Davidbick/PowerMesh/Home Assistant Docs/Matter Standard.pdf

What is the Matter Standard

Matter is an open-source communication standard for smart home devices. It was created to unify proprietary smart devices such as Apple, Google, Amazon, and Samsung to talk with each other. Essentially, it allows you to mix and match smart home devices and hubs among top brands and for any other brand that adopts the Matter standard.

How Matter works

If something has the Matter standard, then it has standardized commands. This would mean a hub and a smart bulb from two different brands will share the same commands, so the bulb will understand the command sent from the hub.

For connectivity, each device should have their own IPv6 address. Matter works with Wi-Fi, thread, and Bluetooth.

Matter locality

Matter works locally first, so it doesn’t require the cloud or internet to function. If the devices receive power, the hub should be able to send commands to the smart device. The smart devices that receive the command should also function the same.

Security

[add information about distributed compliance ledger]

[add info about encryption]
