Davidbick/PowerMesh/Home Assistant Docs/Home Assistant.pdf

## Home Assistant

What it is

Home Assistant is an open-source software that is meant for home automation. Compared to other smart hubs, Home Assistant excels in privacy/security and reliability. This is because Home Assistant relies on the local area network (LAN). If the Wi-Fi is down but power is still available, Home Assistant can still issue commands over LAN. In the chance that LAN is not available, Home Assistant also works with Zigbee and Z-Wave devices which use mesh networks. Since everything is local and is not part of the cloud, it is private and secure.

Another power of Home Assistant is that since it works with Zigbee, Z-Wave, Wi-Fi, and Bluetooth, it can integrate many different products together. If a Bluetooth device is triggered, Home Assistant will be notified and can tell a Zigbee device to do something depending on that state of the Bluetooth device. This allows for powerful pairings of devices that can’t communicate with each other.

If a device only works with the cloud, Home Assistant can communicate with the cloud too, but it requires internet.

What is needed

For Home Assistant to work, it needs dedicated hardware that is always running. This can be a laptop turned into a server, a Raspberry Pi (RPI), or Home Assistant’s own hardware (Home Assistant Green or Yellow [Note: Yellow is discontinued but is still receiving software updates]). For the Raspberry Pi route, USB dongles would have to be installed for Zigbee/Z-wave and maybe even Bluetooth (since the Pi’s Bluetooth might not be strong enough). For Home Assistant Green, it works on the internet and LAN but doesn’t come with Zigbee/Z-Wave. It is essentially made for plug-and-play. Home Assistant Yellow features more capabilities like Zigbee and Z-Wave. It also supports Thread, which uses Matter. However, it costs more.

Another note for using Raspberry Pi is the difference between RPI3, RPI4, and RPI5. RPI3 can handle Home Assistant, but its capabilities are limited, such as its 1 GB of RAM. For a little more money, RPI4 is a direct upgrade to RPI3. RPI4 has the option to be bought with 4 GB which would be useful if installing apps/add-ons for Home Assistant. It also has 2 USB3 ports, which are much better than USB2. With the USB3 ports, a SATA SSD can be added with a USB to SATA connector. A SATA SSD will offer more reliability and speed compared to a MicroSD card. For the RPI5, it needs active cooling. While the RPI5 has more capabilities than the RPI4, we probably don’t need that performance for our project.

How to connect to Home Assistant

How Home Assistant get statuses of devices

Some devices may report their statuses to Home Assistant. However, some devices don’t. To get the status of these devices, Home Assistant polls the device for their status every certain amount of time.
