Davidbick/PowerMesh/General_ST_Docs/ST_Eval_Files/EVALKITST8500-1 PCB Layout/PSU_VIPER_BOARD_HV_rev251/PSU_VIPER_BOARD_HV-Rev2-assy_top+track.pdf

PCB 1

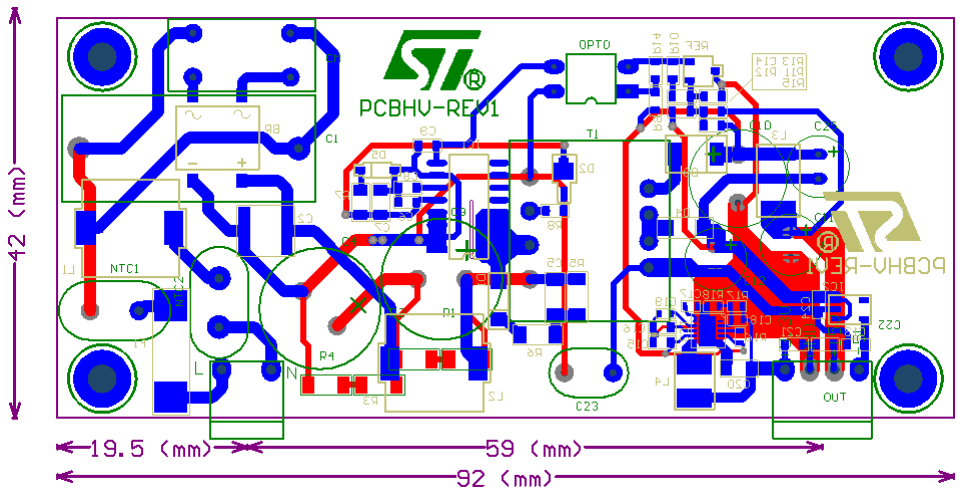
[picture p9: figure]
