Davidbick/PowerMesh/General_ST_Docs/ST_Eval_Files/EVLKST8500GH-2_Schematics/Schematic files/EVALMODST8500-1-Rev421-schematic.pdf

ST8500

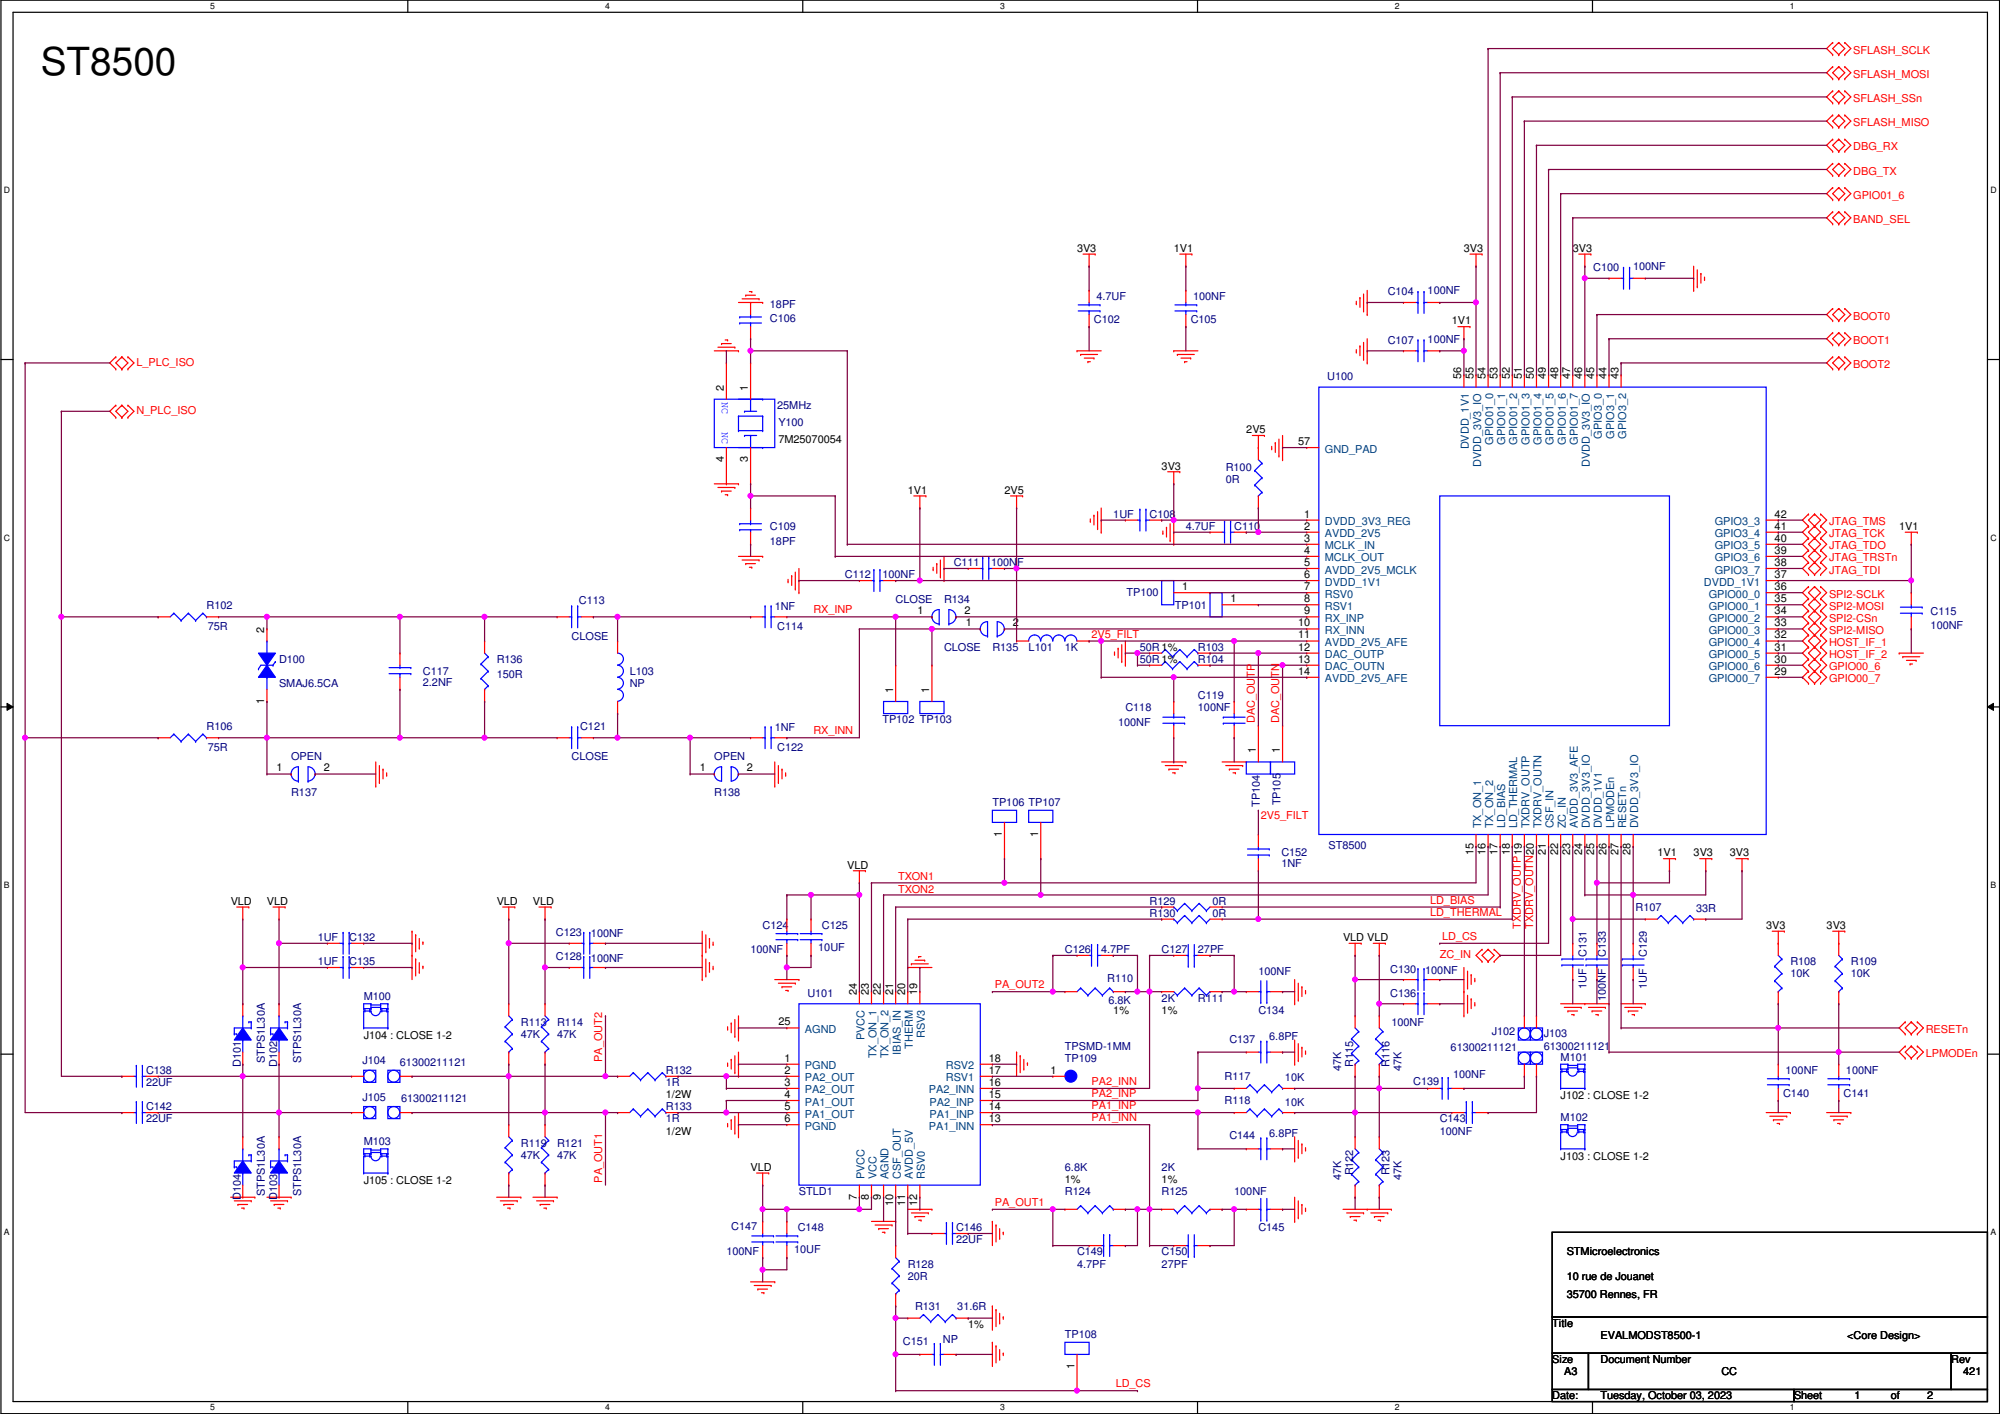
[picture p14: page 1]

# Board to Board Connector - Digital

# SERIAL FLASH

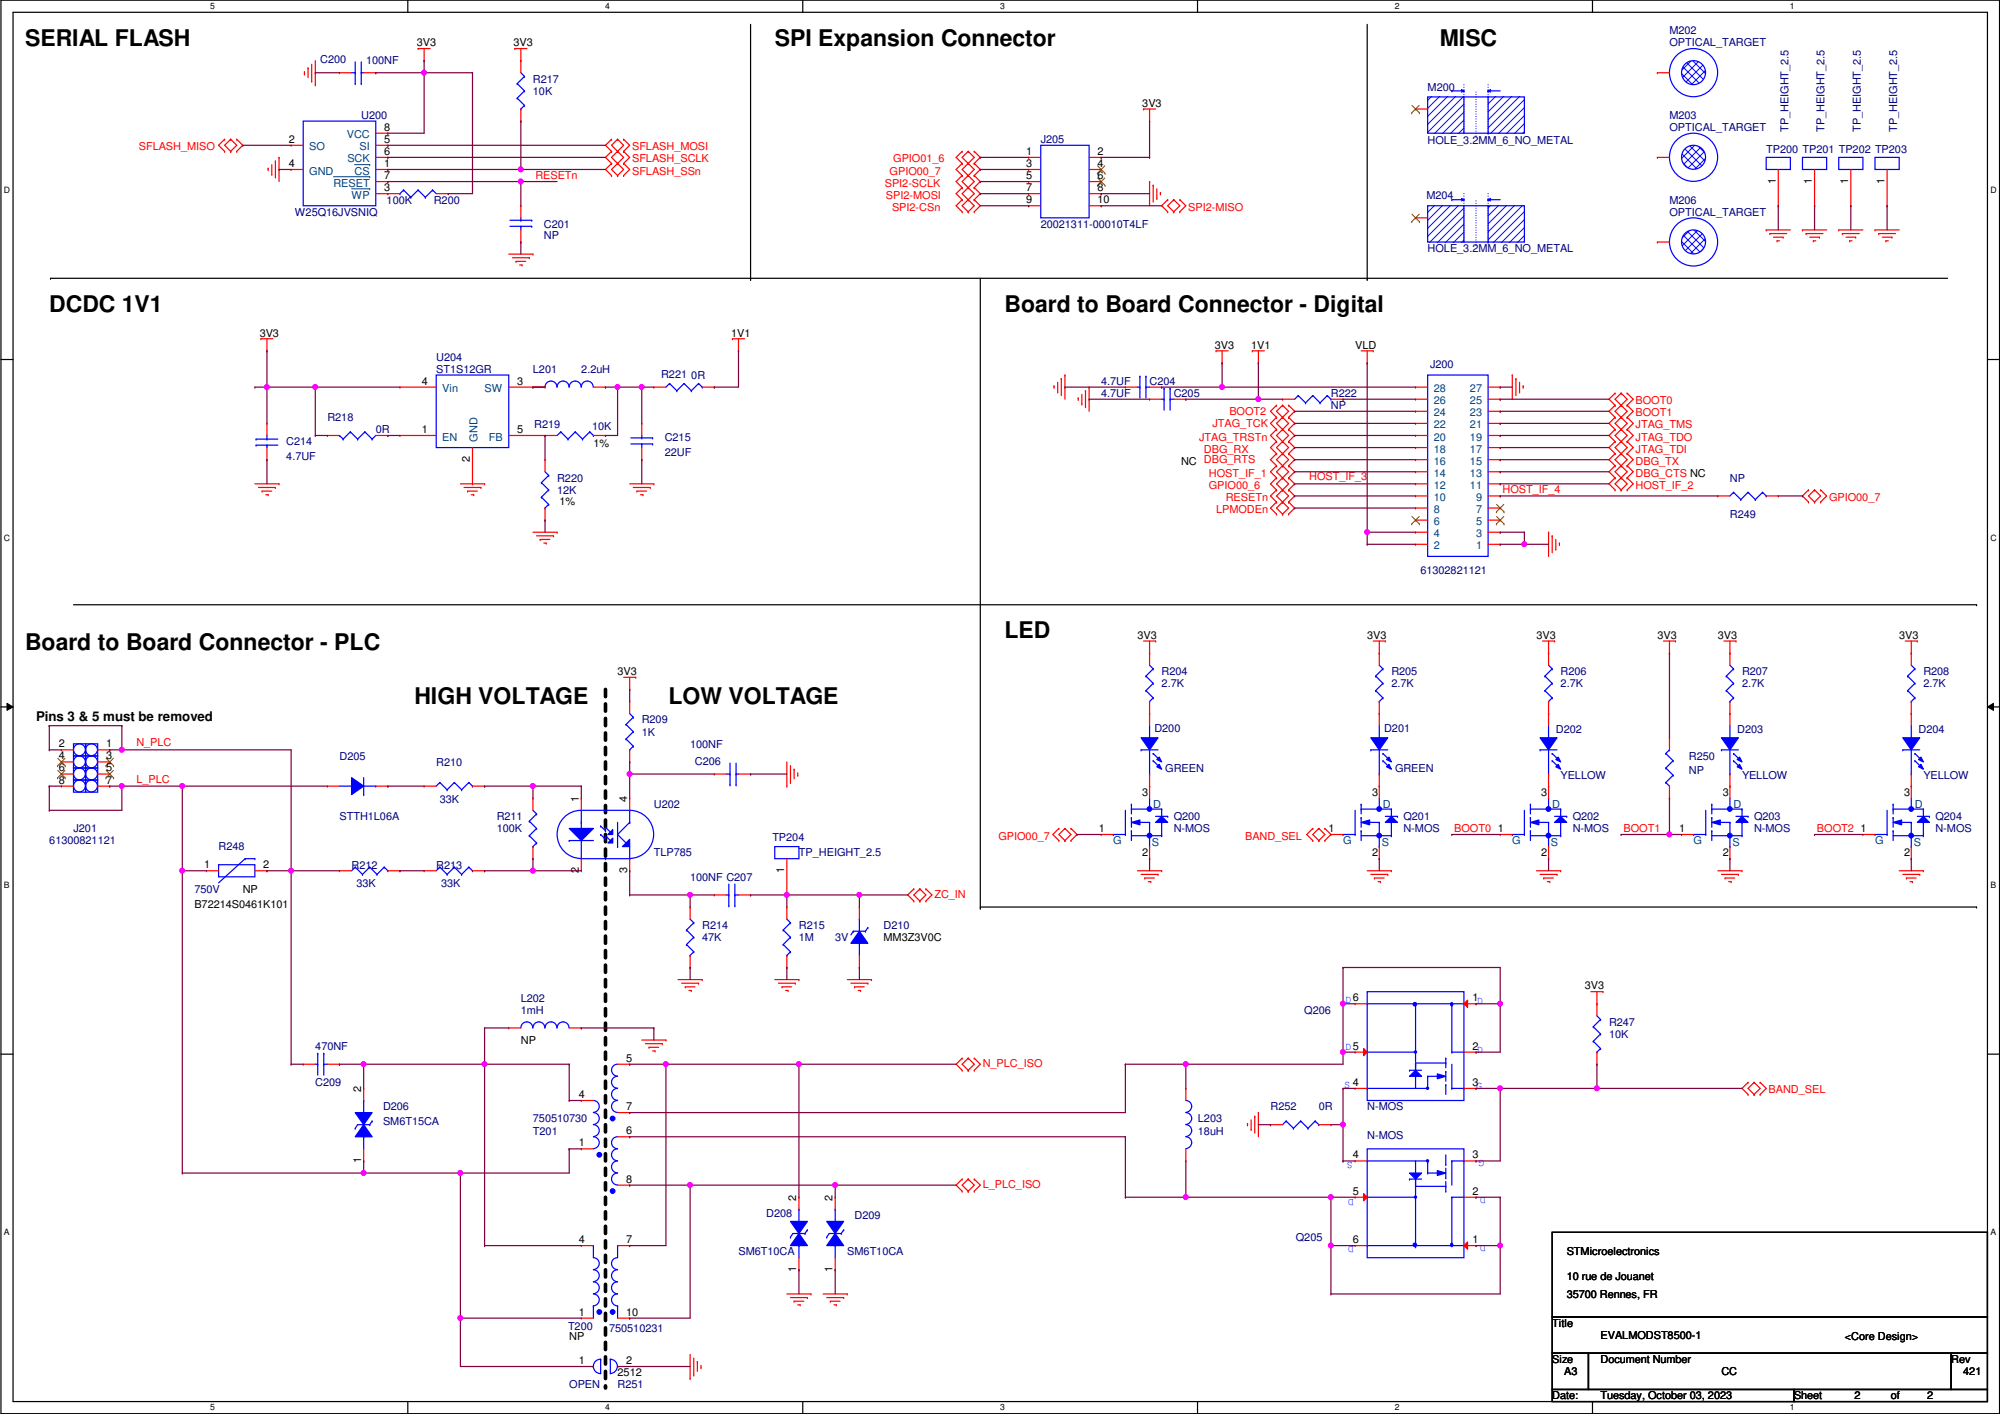
[picture p15: page 2]

Board to Board Connector - PLC

Pins 3 & 5 must be removed
