Davidbick/PowerMesh/Digital_Board/STM_PLC_Board/STM_PLC_Board.pdf

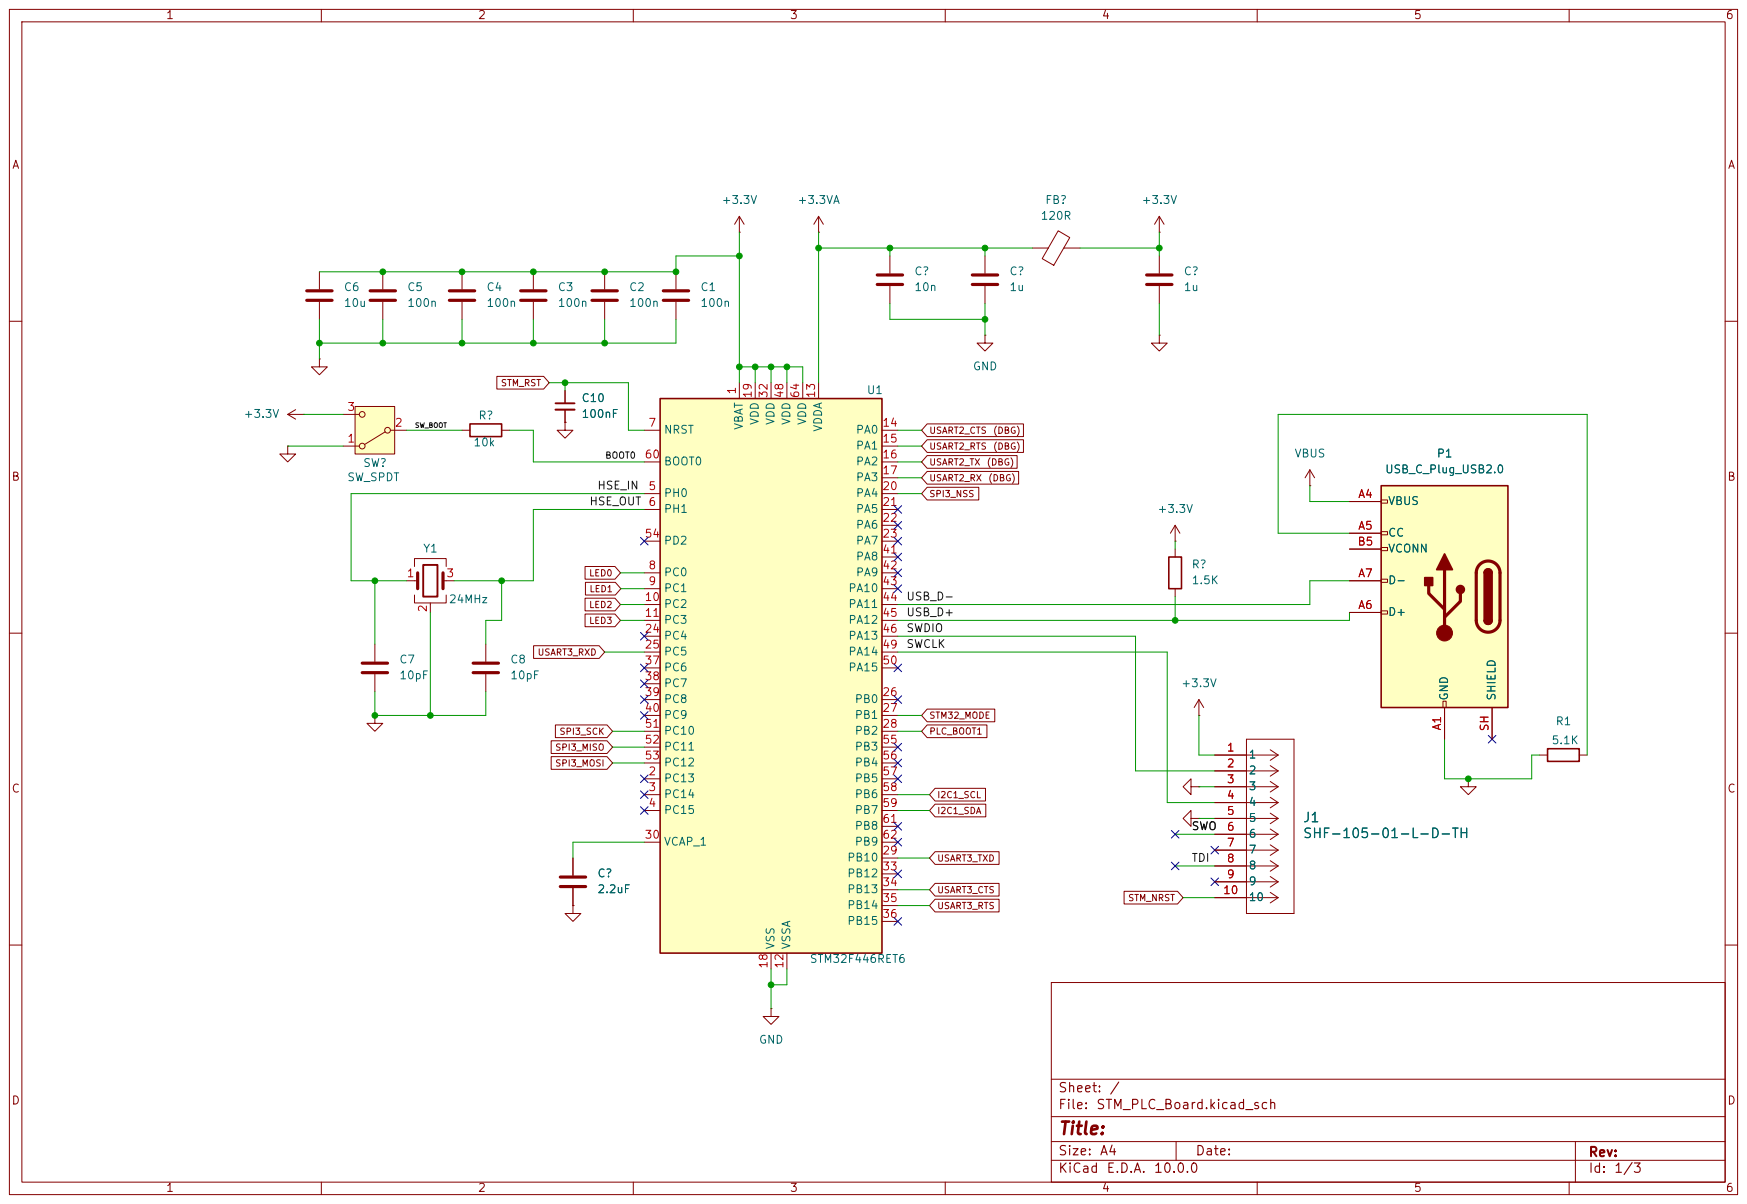
[picture p16: page 1]

Size: A4 | Rev:
KiCad E.D.A. 10.0.0 | Id: 1/3

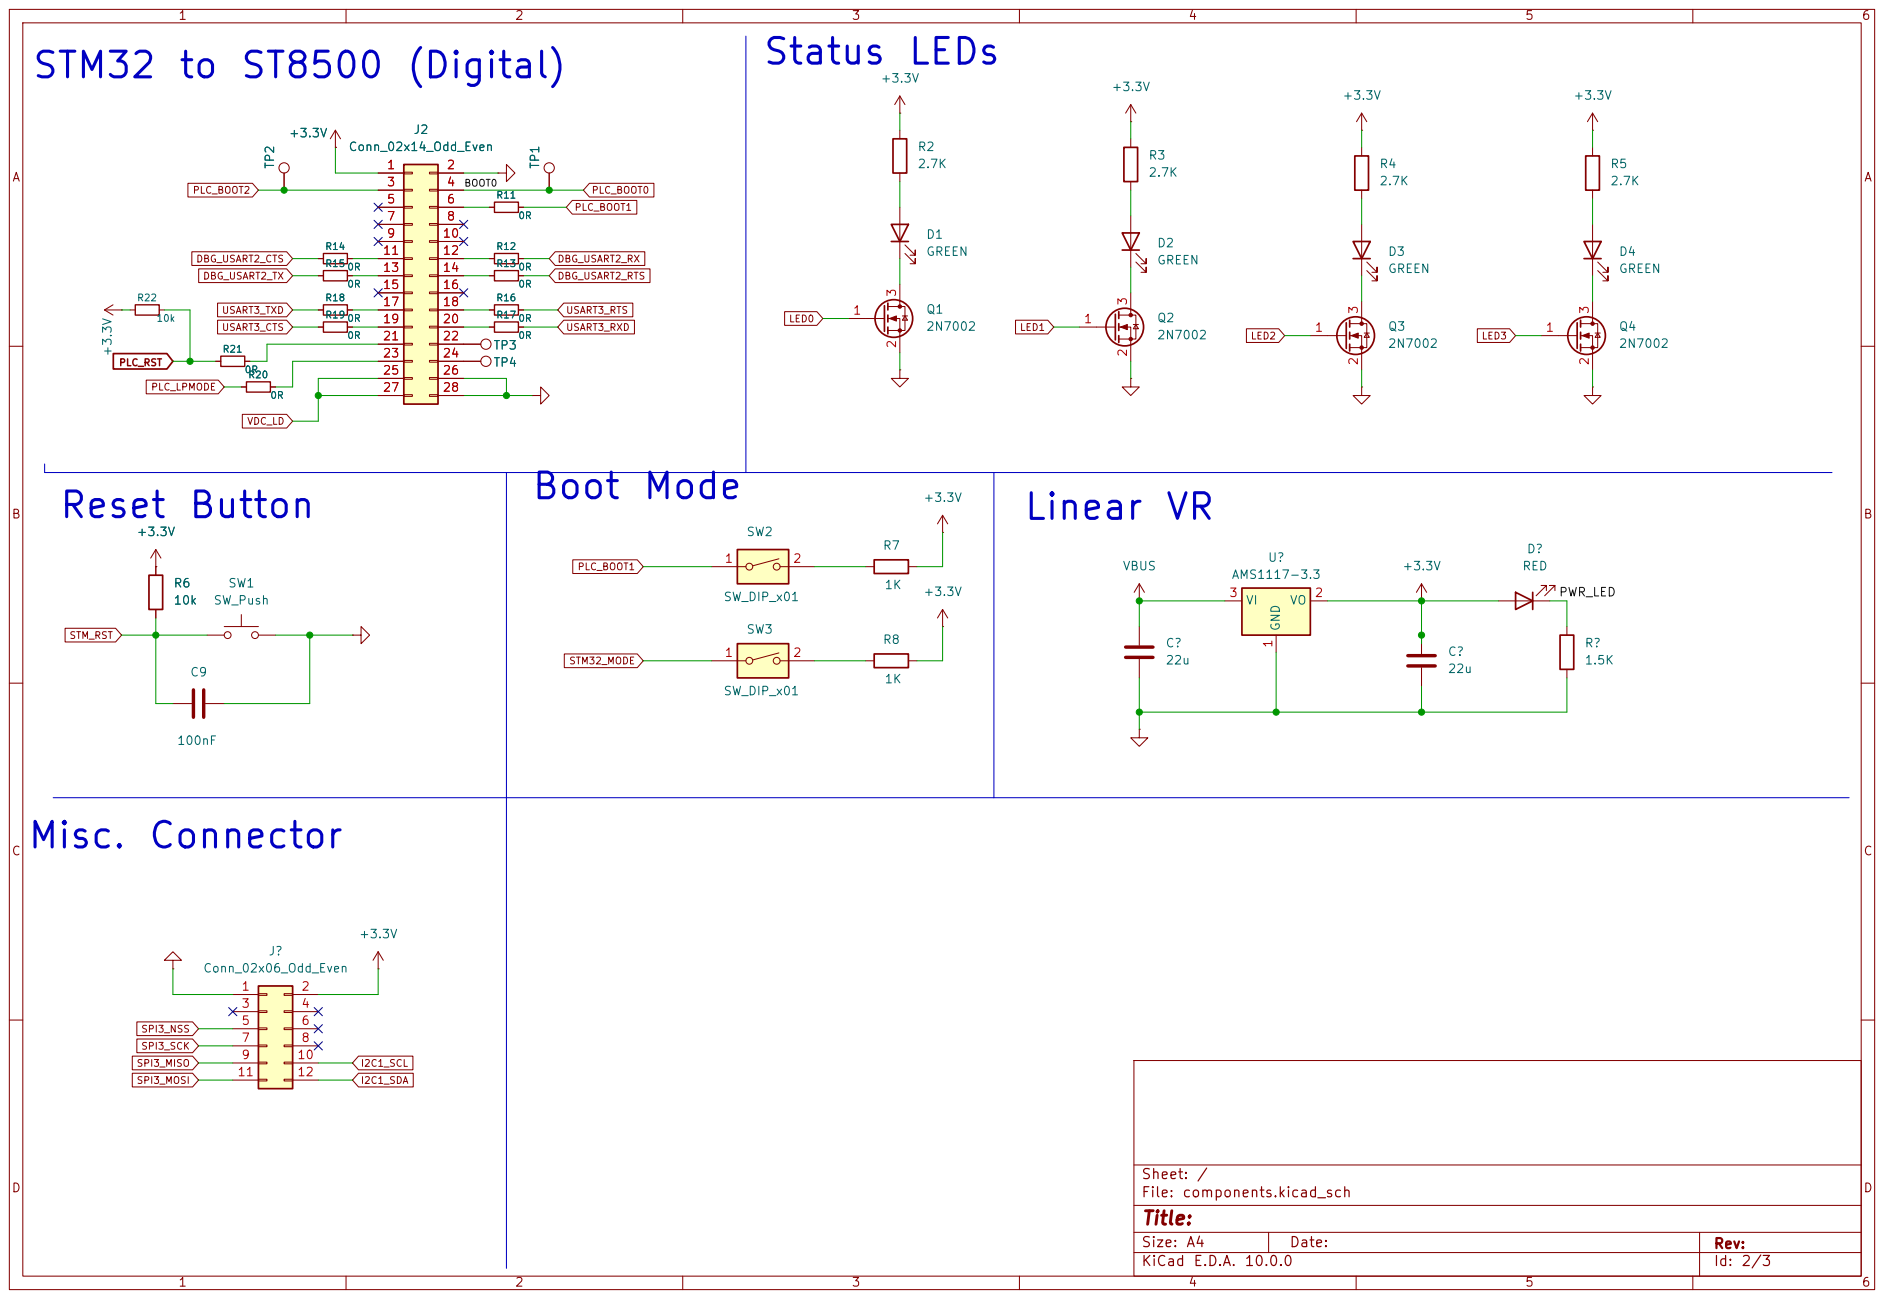
[picture p17: page 2]

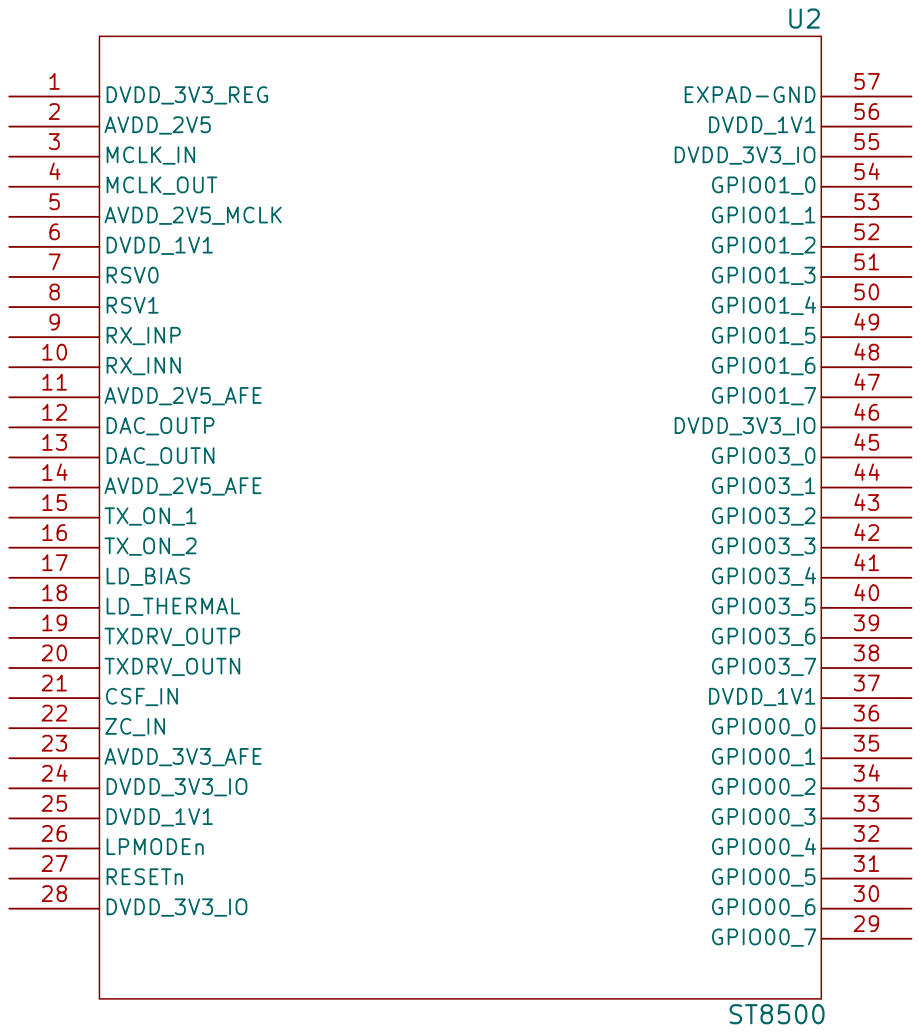
[picture p18: page 3]
