Davidbick/PowerMesh/General_ST_Docs/ST_Eval_Files/EVLKST8500GH-2_Schematics/Schematic files/EVALS2915A2-schematic.pdf

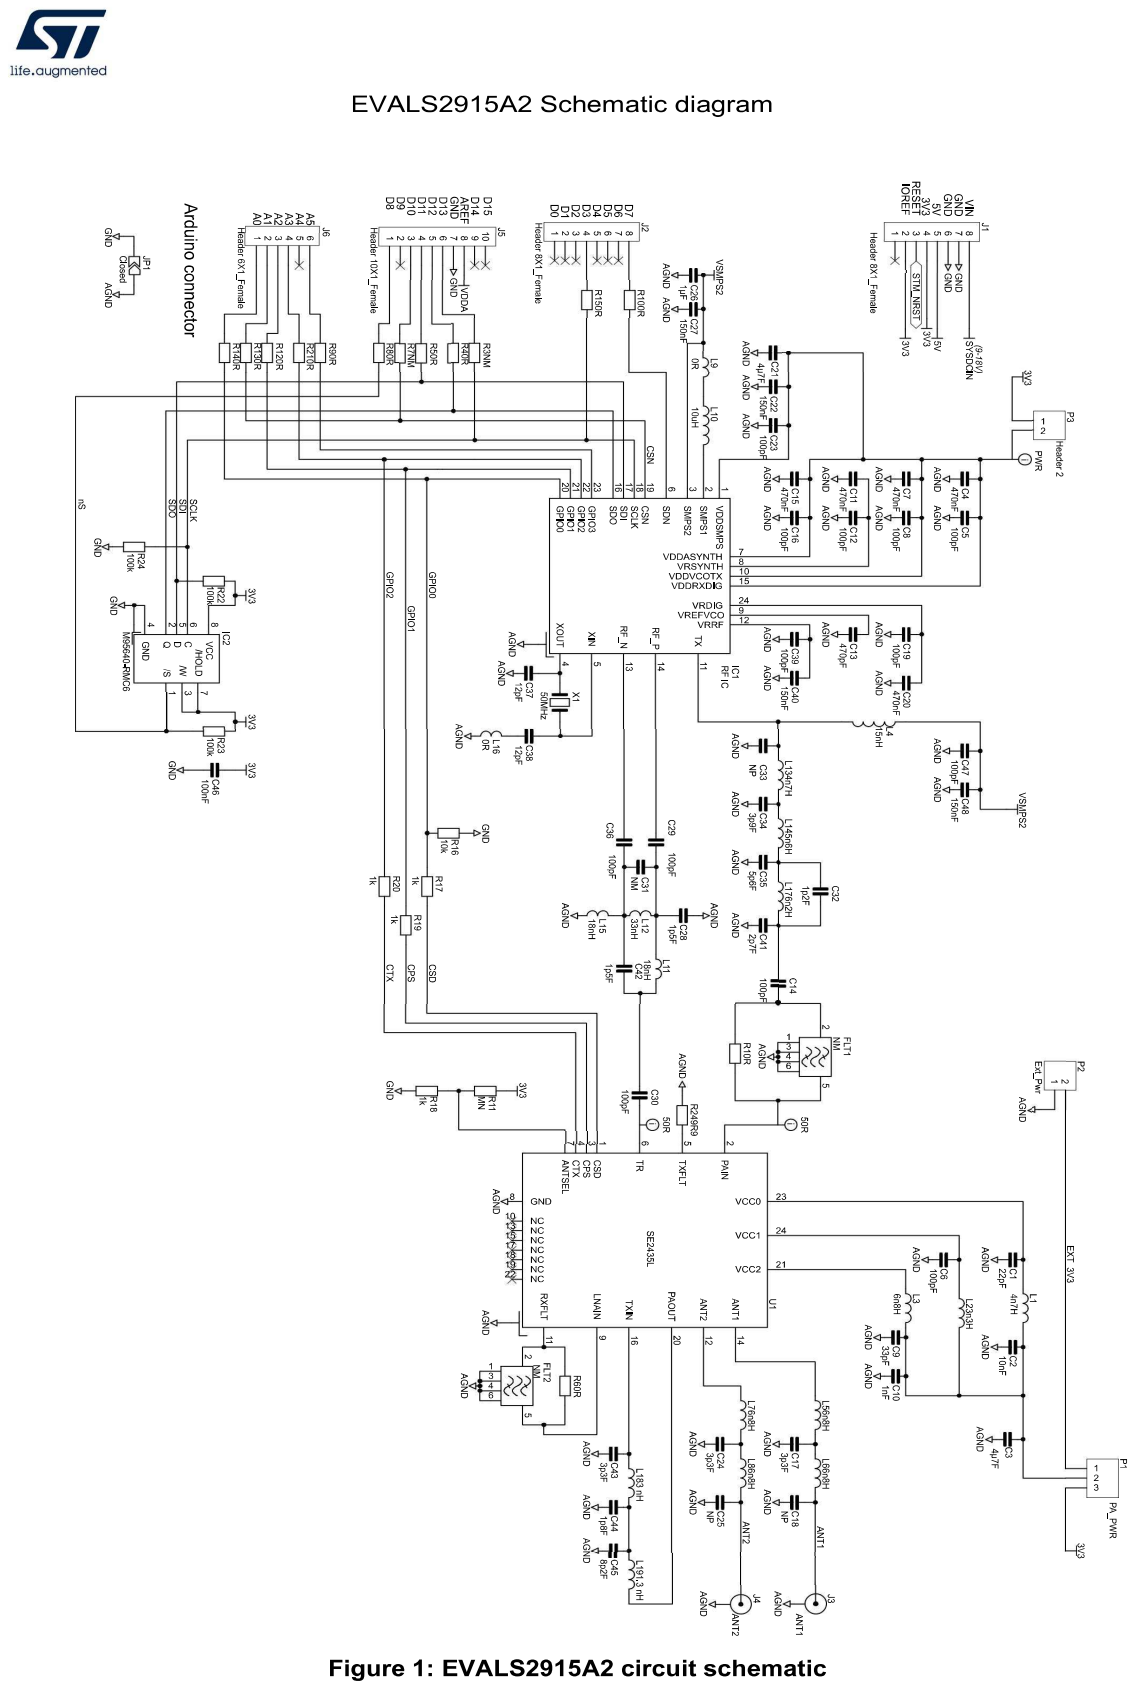
[picture p19: page 1]
