Davidbick/PowerMesh/General_ST_Docs/ST_Eval_Files/EVALKITST8500-1 Schematics/PSU_VIPER_BOARD_HV_rev241/PSU_VIPER_BOARD_HV-Rev241-Sch.pdf

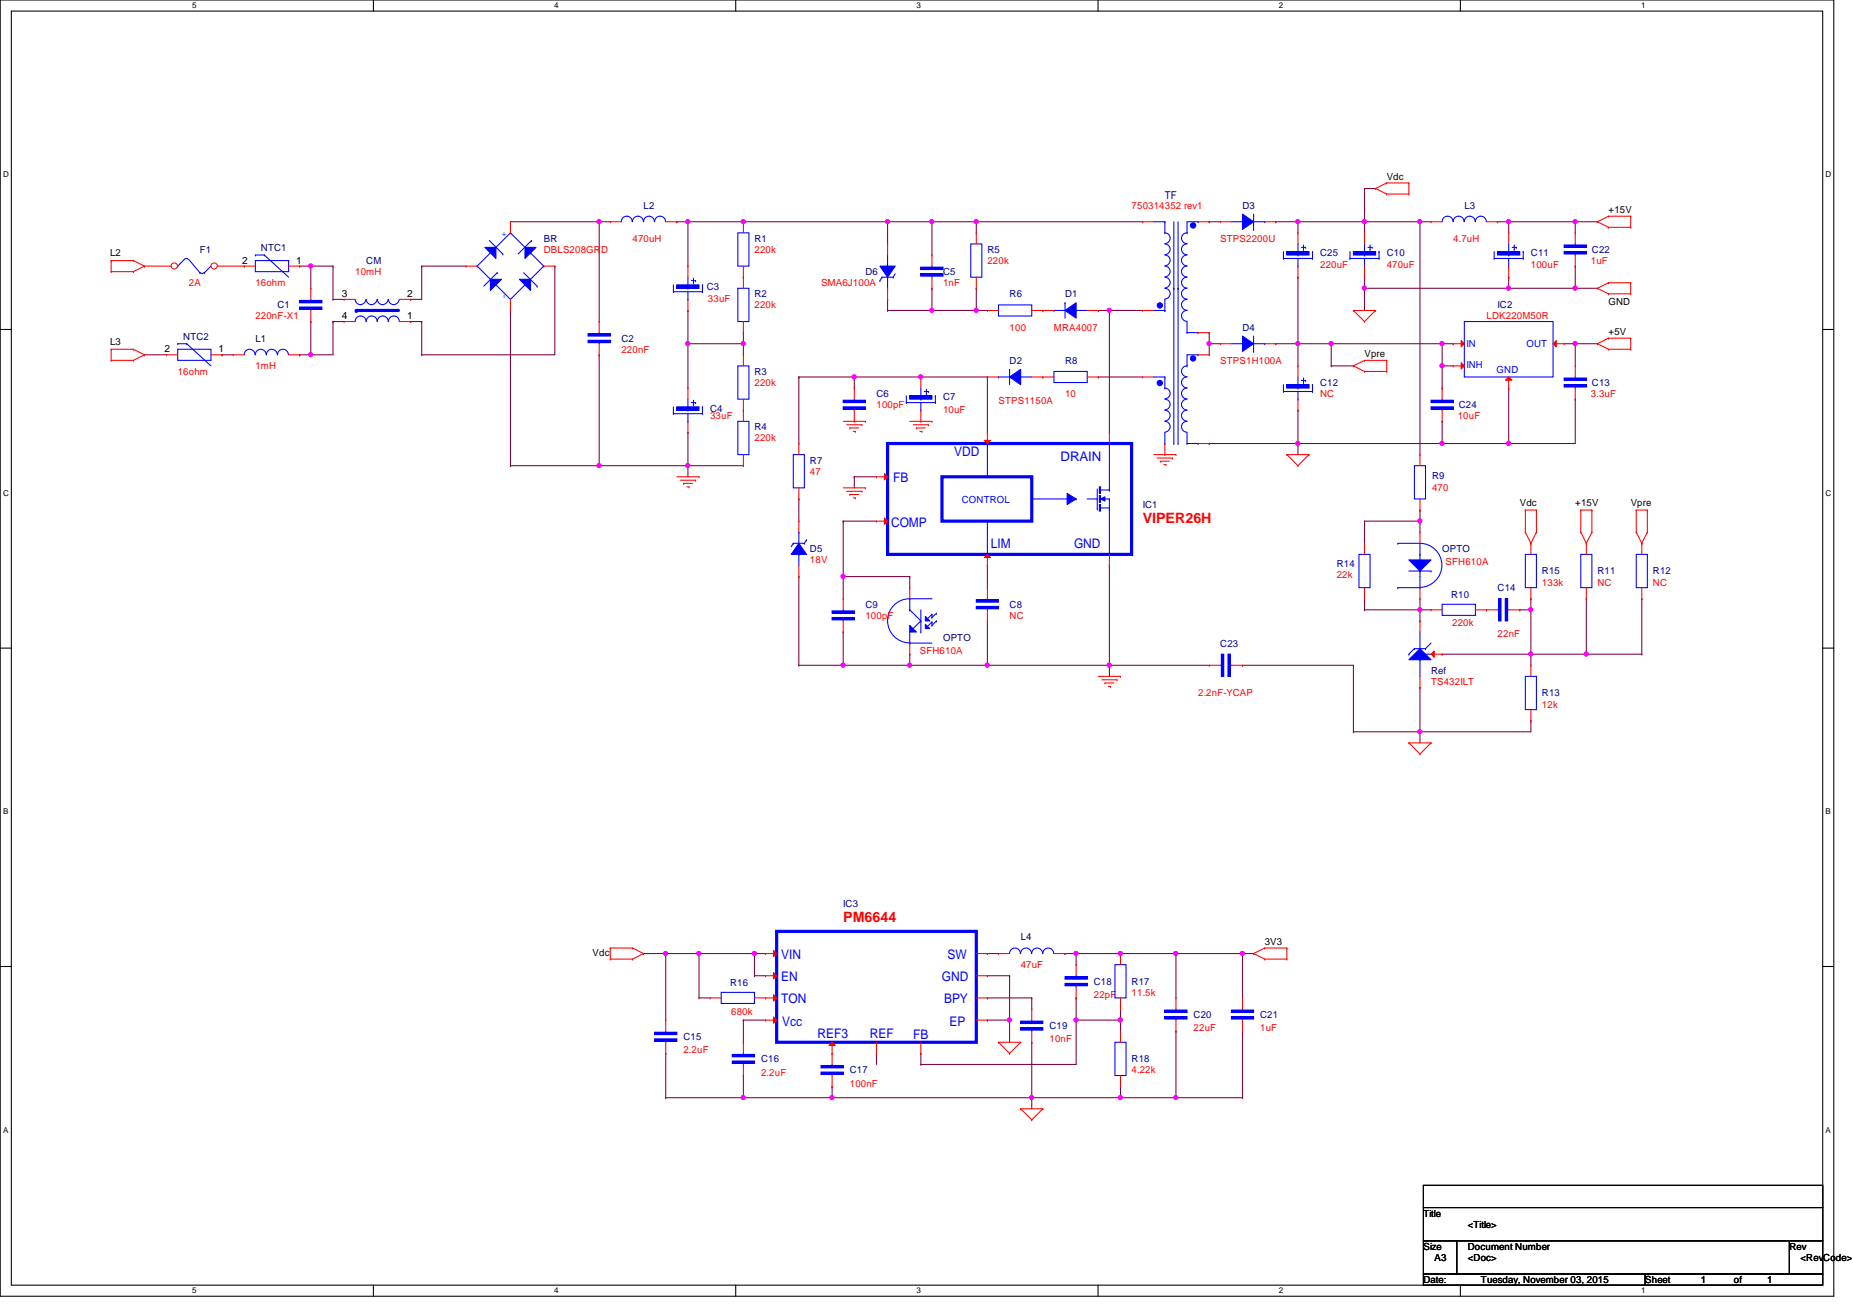
[picture p20: page 1]
