Davidbick/PowerMesh/General_ST_Docs/ST_Eval_Files/EVALKITST8500-1 PCB Layout/EVALST-PLCMB1_CJ-Rev211/EVALST-PLCMB1_CJ-Rev2-assy_top+track.pdf

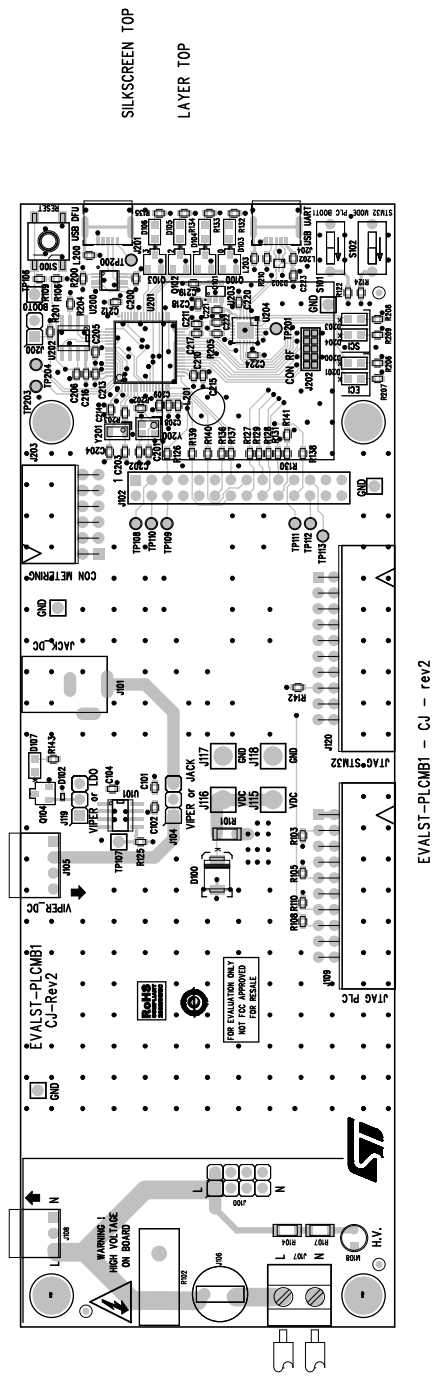
[picture p21: page 1]
