Davidbick/PowerMesh/STM32/Projects/stm32_to_st8500_test/Core/Src/main.c

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
/* Includes ------------------------------------------------------------------*/
#include "main.h"

/* USER CODE BEGIN PD */
#define ST8500_SYNC_BYTE       0x16
#define ST8500_MODE            0xFE

#define ST8500_CMD_MIB_GET     0x21

#define ST8500_MIB_BOOT_VER    0x04

#define ST8500_TIMEOUT_MS      500
/* USER CODE END PD */

UART_HandleTypeDef huart2;

void SystemClock_Config(void);
static void MX_GPIO_Init(void);
static void MX_USART2_UART_Init(void);
/* USER CODE BEGIN PFP */
static uint16_t ST8500_CRC16_XMODEM(const uint8_t *data, uint16_t length);
static HAL_StatusTypeDef ST8500_ReadBootVersion(uint32_t *bootVersion);
/* USER CODE END PFP */

  /* USER CODE BEGIN 0 */
  /*
  * Calculate CRC-16/XMODEM.
  *
  * ST's ST8500 host interface uses CRC protection on messages.
  * This implementation can later be reused for additional
  * ST8500 commands.
  */
  static uint16_t ST8500_CRC16_XMODEM(const uint8_t *data, uint16_t length)
  {
      uint16_t crc = 0x0000;

      for (uint16_t i = 0; i < length; i++)
      {
          crc ^= ((uint16_t)data[i] << 8);

          for (uint8_t bit = 0; bit < 8; bit++)
          {
              if (crc & 0x8000)
              {
                  crc = (crc << 1) ^ 0x1021;
              }
              else
              {
                  crc <<= 1;
              }
          }
      }

      return crc;
  }


  /*
  * Ask the ST8500 bootloader for its boot version.
  *
  * Returns HAL_OK if a valid ST8500 response is received.
  */
  static HAL_StatusTypeDef ST8500_ReadBootVersion(uint32_t *bootVersion)
  {
      /*
      * MIB_Get request:
      *
      * [0..1]  Sync
      * [2]     Command ID
      * [3..4]  Message length
      * [5]     Mode
      * [6..9]  State/reserved
      * [10]    MIB attribute
      * [11..12] CRC
      */

      uint8_t txBuffer[13] = {0};

      txBuffer[0] = ST8500_SYNC_BYTE;
      txBuffer[1] = ST8500_SYNC_BYTE;

      txBuffer[2] = ST8500_CMD_MIB_GET;

      /* Payload contains one byte: the MIB ID */
      txBuffer[3] = 0x01;
      txBuffer[4] = 0x00;

      txBuffer[5] = ST8500_MODE;

      /* State field for request */
      txBuffer[6] = 0x00;
      txBuffer[7] = 0x00;
      txBuffer[8] = 0x00;
      txBuffer[9] = 0x00;

      /* Request ST8500 bootloader version */
      txBuffer[10] = ST8500_MIB_BOOT_VER;

      uint16_t crc = ST8500_CRC16_XMODEM(txBuffer, 11);

      /* CRC is transmitted little-endian */
      txBuffer[11] = (uint8_t)(crc & 0xFF);
      txBuffer[12] = (uint8_t)((crc >> 8) & 0xFF);

      /*
      * Boot version MIB is four bytes, so the expected
      * complete response is 16 bytes.
      */
      uint8_t rxBuffer[16] = {0};

      HAL_StatusTypeDef status;

      status = HAL_UART_Transmit(
          &huart2,
          txBuffer,
          sizeof(txBuffer),
          ST8500_TIMEOUT_MS
      );

      if (status != HAL_OK)
      {
          return status;
      }

      status = HAL_UART_Receive(
          &huart2,
          rxBuffer,
          sizeof(rxBuffer),
          ST8500_TIMEOUT_MS
      );

      if (status != HAL_OK)
      {
          return status;
      }

      /* Check synchronization bytes */
      if ((rxBuffer[0] != ST8500_SYNC_BYTE) ||
          (rxBuffer[1] != ST8500_SYNC_BYTE))
      {
          return HAL_ERROR;
      }

      /* Response should match our MIB_GET command */
      if (rxBuffer[2] != ST8500_CMD_MIB_GET)
      {
          return HAL_ERROR;
      }

      /*
      * STATE = 0 means ACK.
      * Bytes 6-9 form the four-byte state field.
      */
      if ((rxBuffer[6] != 0x00) ||
          (rxBuffer[7] != 0x00) ||
          (rxBuffer[8] != 0x00) ||
          (rxBuffer[9] != 0x00))
      {
          return HAL_ERROR;
      }

      /*
      * MIB boot version is four bytes.
      * ST8500 protocol uses little-endian fields.
      */
      *bootVersion =
            ((uint32_t)rxBuffer[10])
          | ((uint32_t)rxBuffer[11] << 8)
          | ((uint32_t)rxBuffer[12] << 16)
          | ((uint32_t)rxBuffer[13] << 24);

      return HAL_OK;
  }
/* USER CODE END 0 */

/**
  * @brief  The application entry point.
  * @retval int
  */
int main(void)
{

  /* MCU Configuration--------------------------------------------------------*/

  /* Reset of all peripherals, Initializes the Flash interface and the Systick. */
  HAL_Init();

  /* Configure the system clock */
  SystemClock_Config();

  /* Initialize all configured peripherals */
  MX_GPIO_Init();
  MX_USART2_UART_Init();
  /* USER CODE BEGIN 2 */
  uint32_t st8500BootVersion = 0;

  HAL_GPIO_WritePin(LD2_GPIO_Port, LD2_Pin, GPIO_PIN_RESET);

  HAL_Delay(100);

  if (ST8500_ReadBootVersion(&st8500BootVersion) == HAL_OK)
  {
      /*
      * ST8500 responded successfully.
      * Turn on the Nucleo LED.
      */
      HAL_GPIO_WritePin(LD2_GPIO_Port, LD2_Pin, GPIO_PIN_SET);
  }
  else
  {
      /*
      * No valid response.
      * Leave LED off.
      */
      HAL_GPIO_WritePin(LD2_GPIO_Port, LD2_Pin, GPIO_PIN_RESET);
  }
  /* USER CODE END 2 */

  /* Infinite loop */
  /* USER CODE BEGIN WHILE */
  while (1)
  {
    /* USER CODE END WHILE */

    /* USER CODE BEGIN 3 */
  }
  /* USER CODE END 3 */
}

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
